p-keminer/iot-alarm-system/hardware/pcb/sender/pcb_sender_r3.png

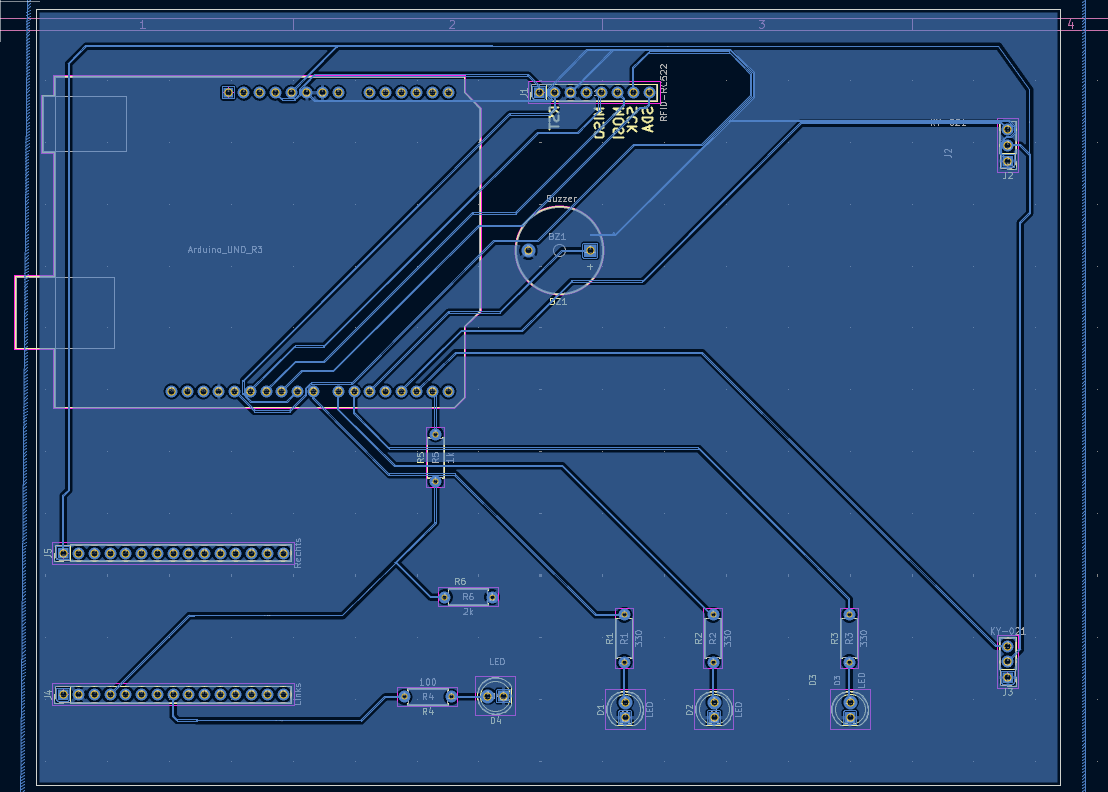
hardware/pcb/sender/pcb_sender_r3.png
