p-keminer/iot-alarm-system/hardware/pcb/sender/pcb_sender_r3_front.png

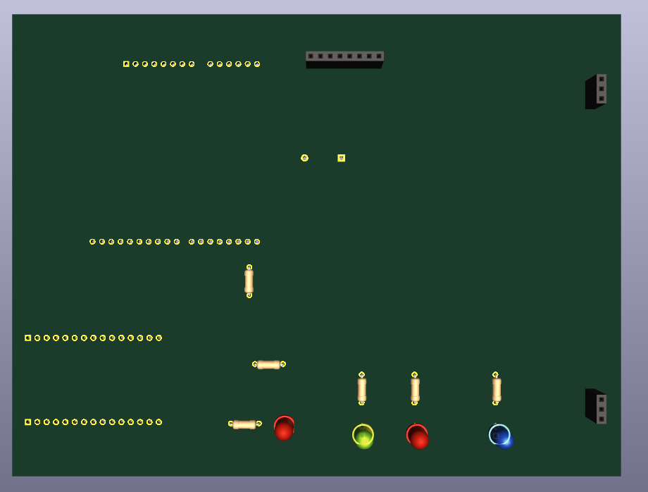
hardware/pcb/sender/pcb_sender_r3_front.png
