p-keminer/iot-alarm-system/hardware/pcb/sender/schematic_sender_r3.png

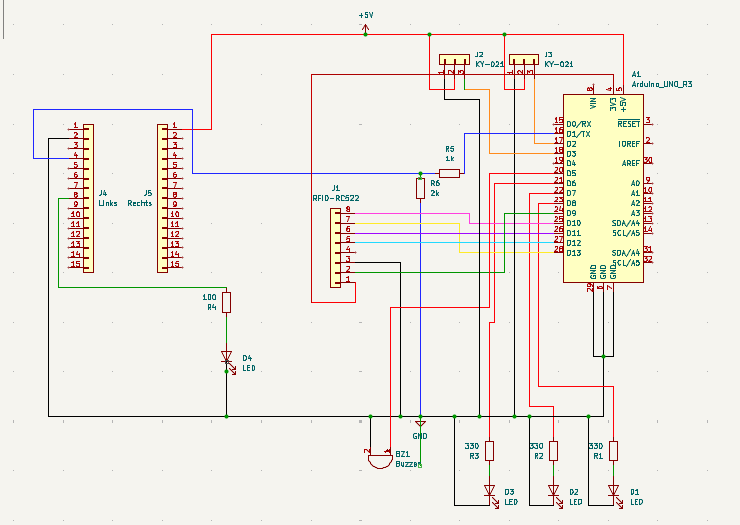
hardware/pcb/sender/schematic_sender_r3.png
