p-keminer/iot-alarm-system/media/photos/prototype_breadboards.png

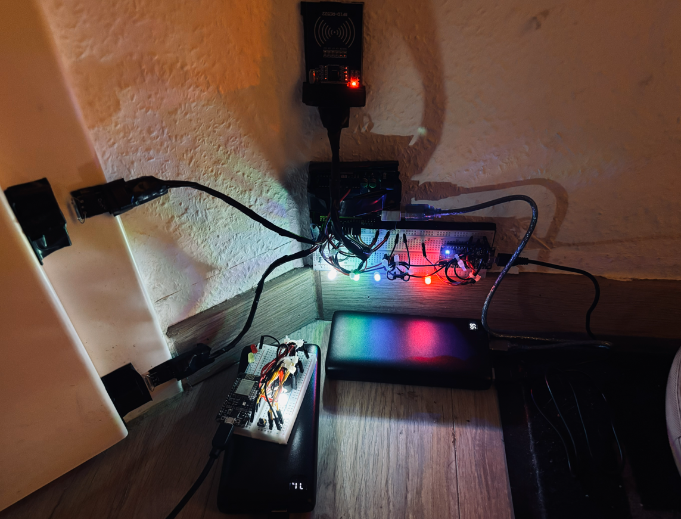
media/photos/prototype_breadboards.png
