p-keminer/iot-alarm-system/media/photos/prototype_housings_3d.jpg

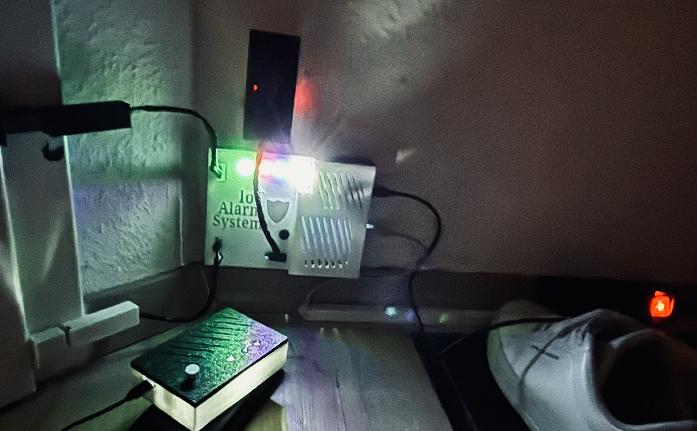
media/photos/prototype_housings_3d.jpg
