p-keminer/iot-alarm-system/media/photos/prototype_perforated_circuit_boards.jpg

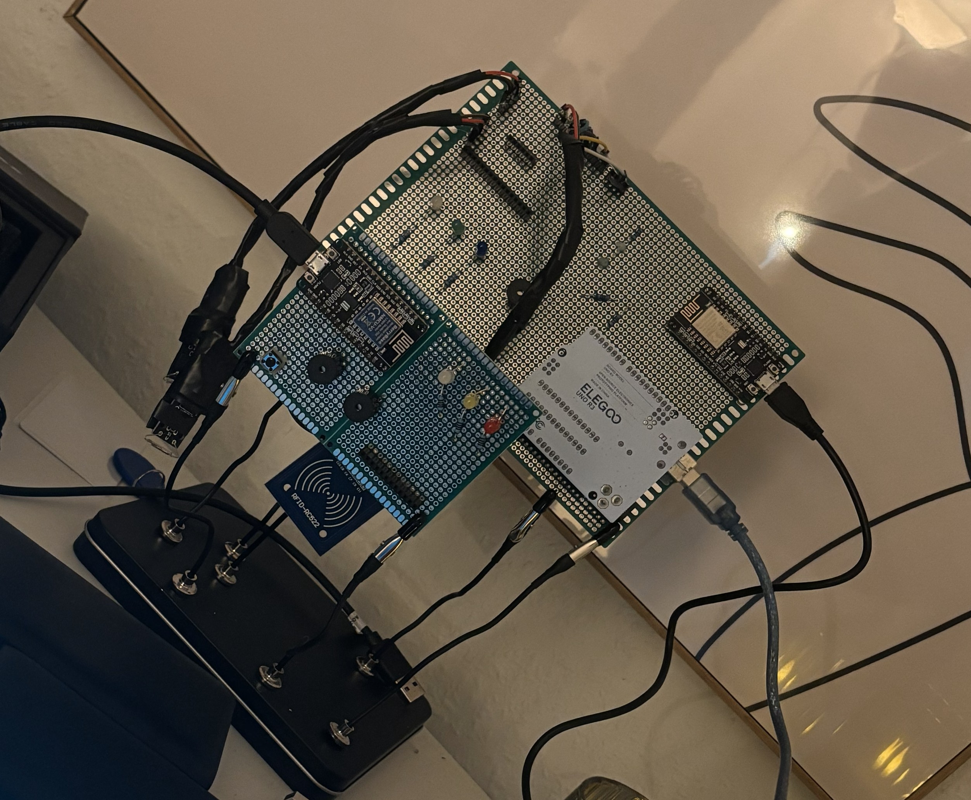
media/photos/prototype_perforated_circuit_boards.jpg
