p-keminer/iot-alarm-system/media/photos/raspberry_pi_zero_2w.jpg

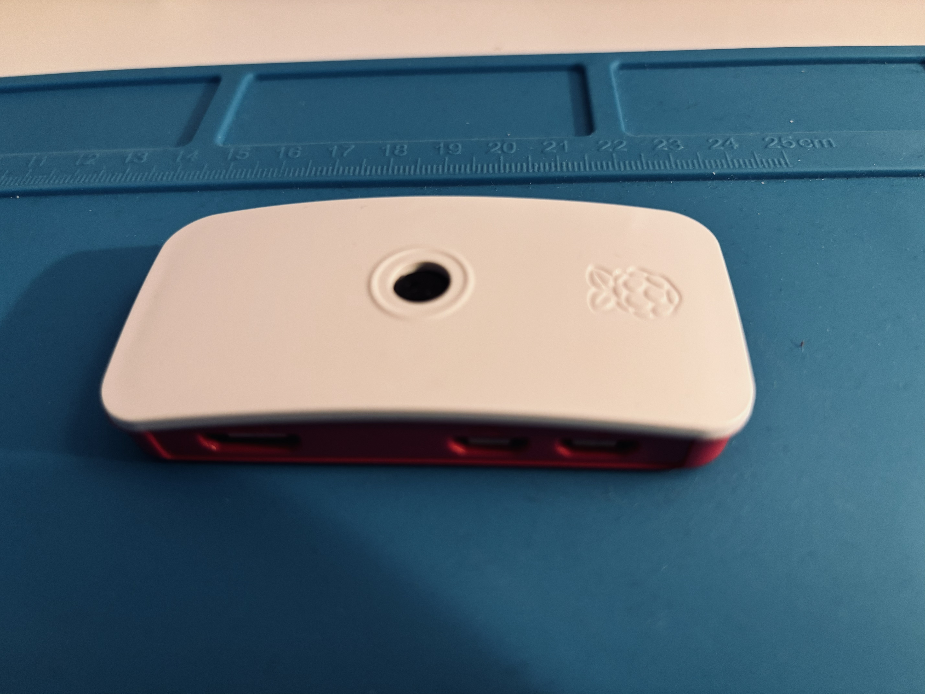
media/photos/raspberry_pi_zero_2w.jpg
