p-keminer/iot-alarm-system/media/photos/raspberrypi.jpg

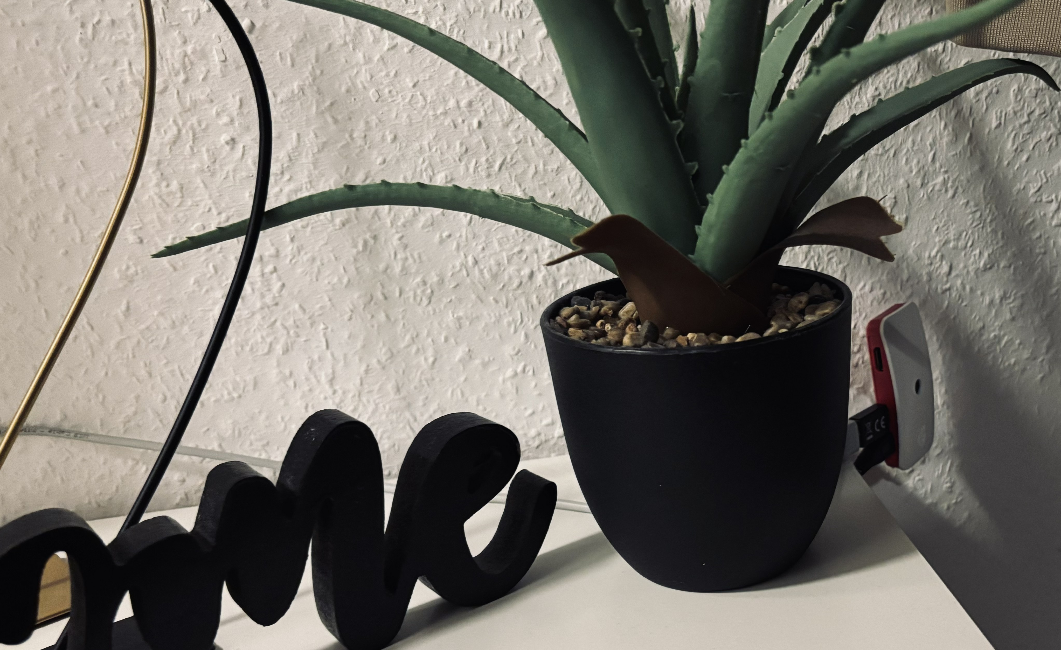
media/photos/raspberrypi.jpg
