p-keminer/iot-alarm-system/media/photos/receiver_enclosure_pcb.jpg

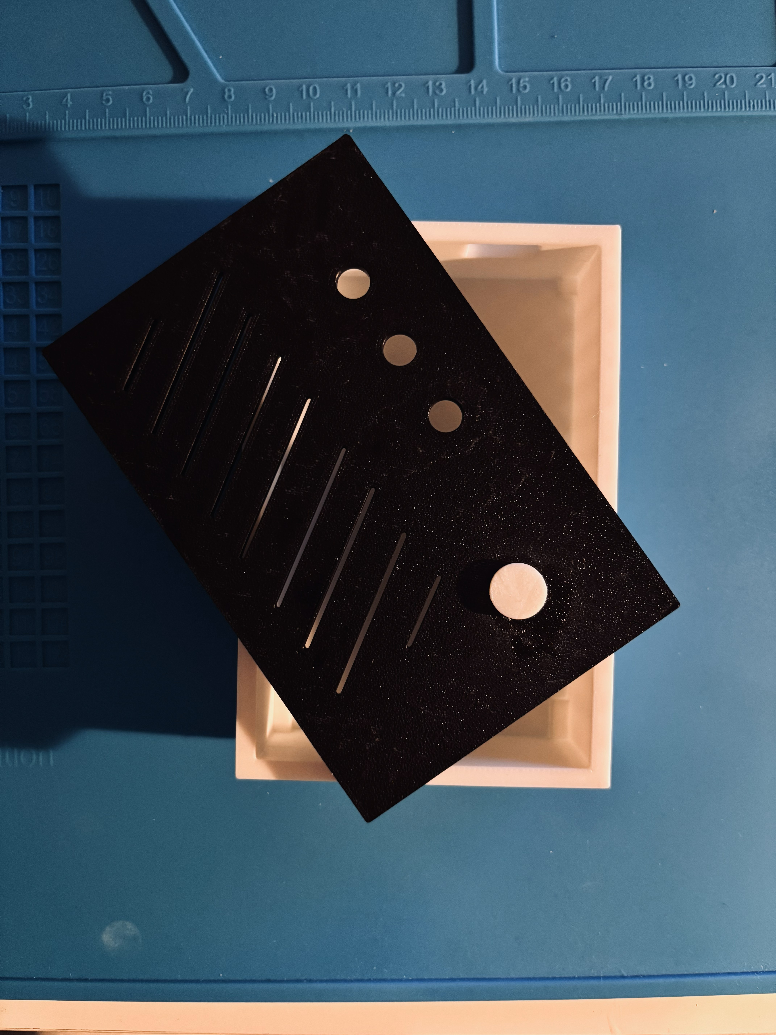
media/photos/receiver_enclosure_pcb.jpg
