p-keminer/iot-alarm-system/media/photos/receiver_pcb.jpg

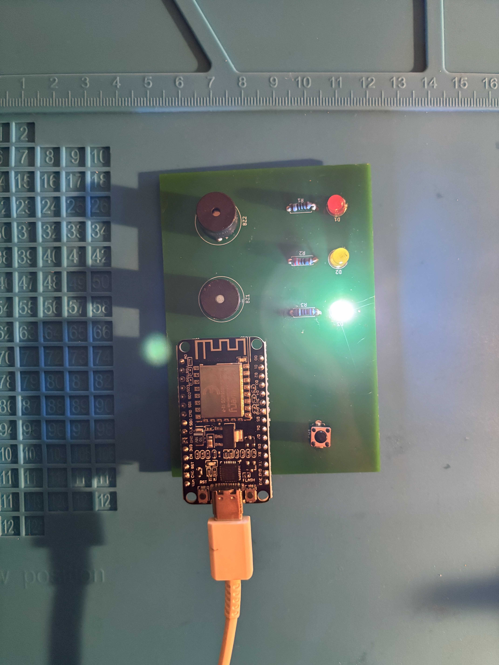
media/photos/receiver_pcb.jpg
