p-keminer/iot-alarm-system/media/photos/sender_enclosure.jpg

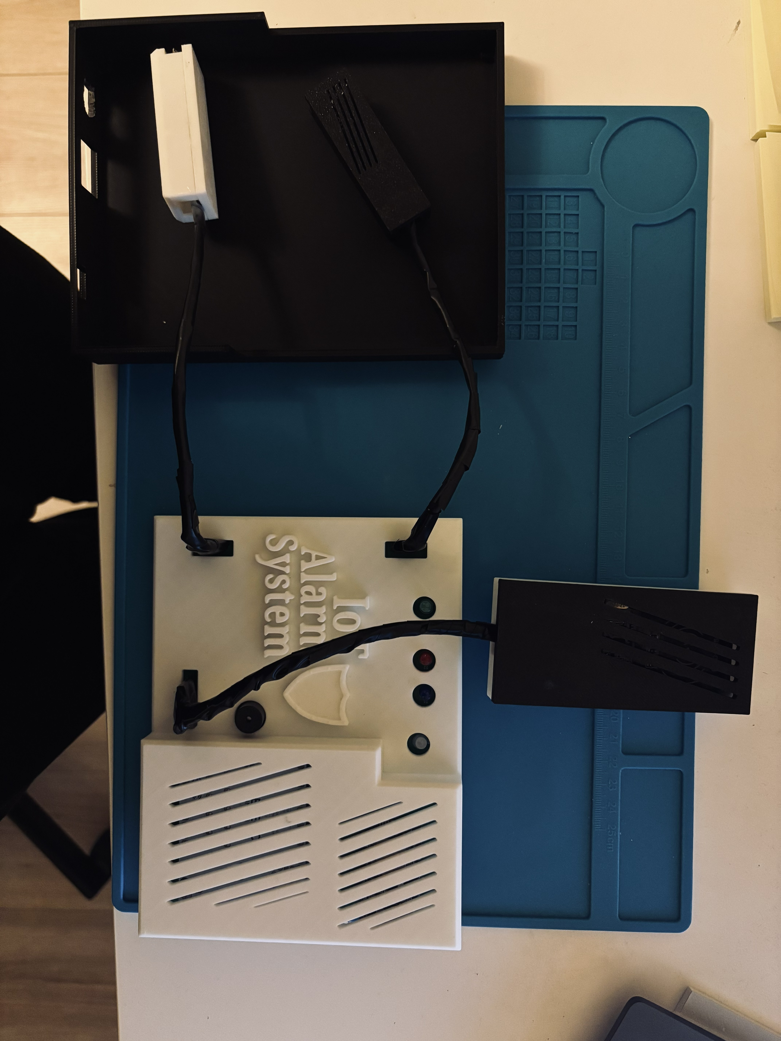
media/photos/sender_enclosure.jpg
