p-keminer/iot-alarm-system/media/photos/sender_pcb.jpg

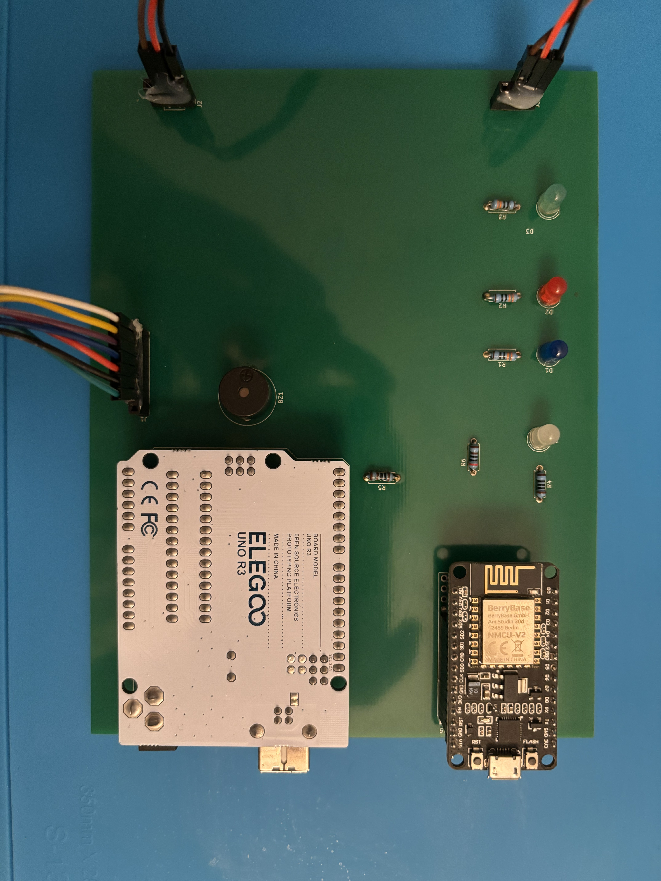
media/photos/sender_pcb.jpg
