p-keminer/iot-alarm-system/media/photos/sensor_enclosure.png

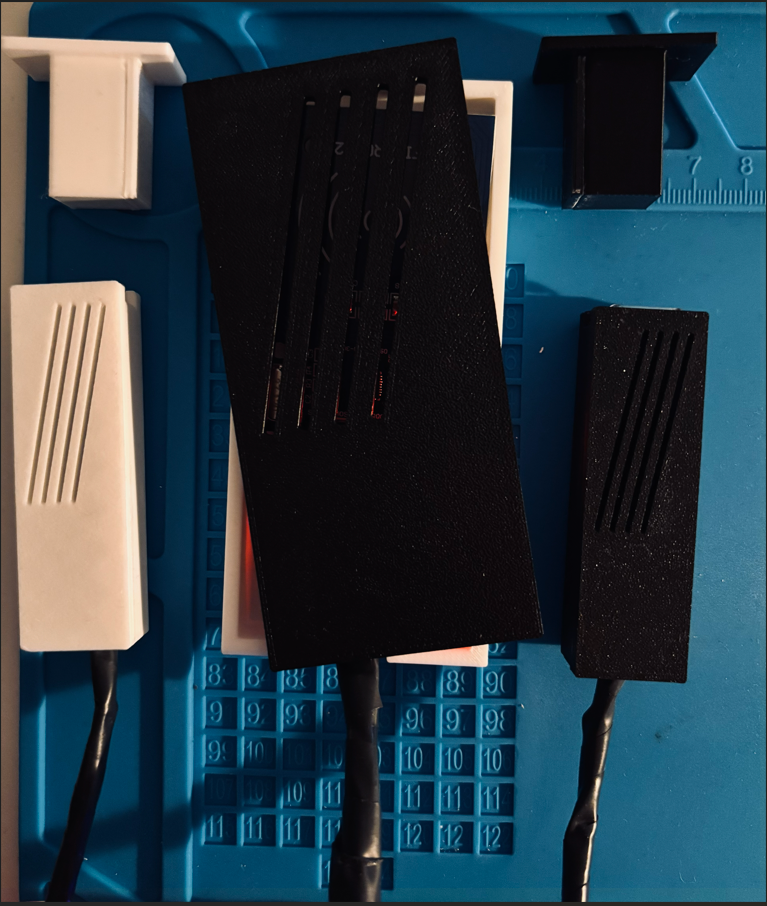
media/photos/sensor_enclosure.png
