p-keminer/iot-alarm-system/media/videos/gifs/receiver_pcb.gif

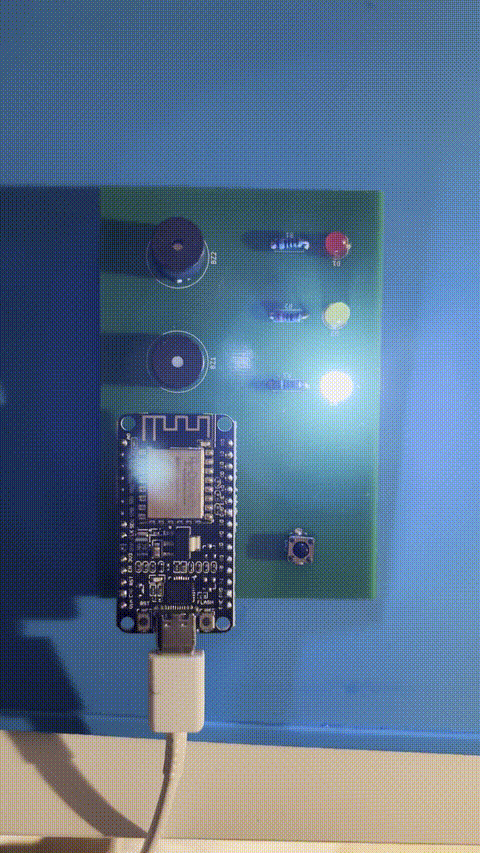
media/videos/gifs/receiver_pcb.gif
