p-keminer/iot-alarm-system/media/videos/gifs/sender_r3_pcb.gif

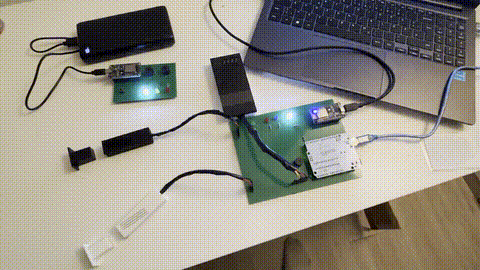
media/videos/gifs/sender_r3_pcb.gif
