p-keminer/iot-alarm-system/mechanics/prints_3d/receiver/receiver_housing.png

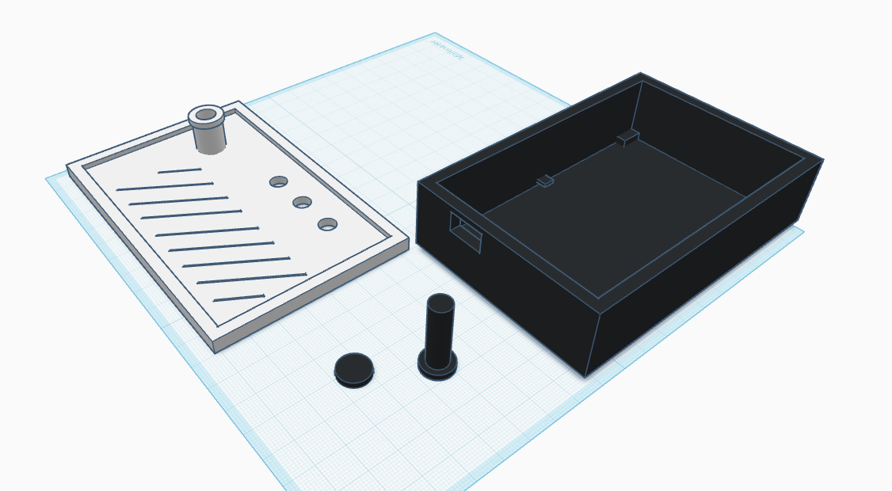
mechanics/prints_3d/receiver/receiver_housing.png
