p-keminer/iot-alarm-system/mechanics/prints_3d/sender/sender_r3_housing.png

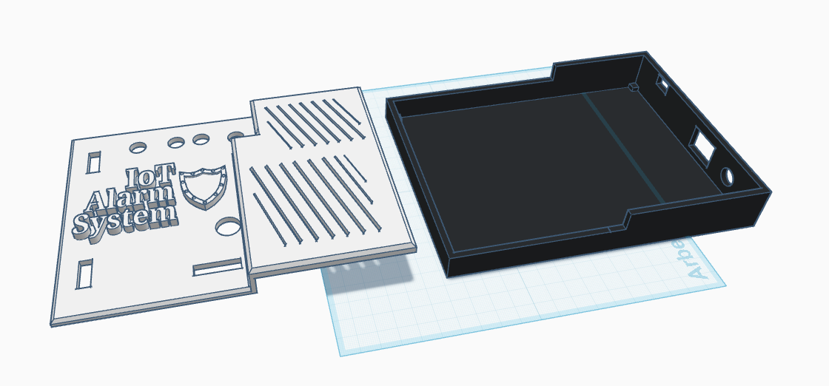
mechanics/prints_3d/sender/sender_r3_housing.png
