p-keminer/iot-alarm-system/firmware/elegoo_uno_r3/sketchR3/alarm_system/hal_rfid.h

// =============================================================================
// hal_rfid.h - Hardwareabstraktion fuer RFID-Leser
// =============================================================================

#ifndef HAL_RFID_H
#define HAL_RFID_H

#include <Arduino.h>

// MFRC522 unterstuetzt 4-, 7- und 10-Byte-UIDs.
#define HAL_RFID_MAX_UID_LEN 10

// Rueckgabewerte beim Kartenlesen
typedef enum {
  RFID_KEINE_KARTE,
  RFID_KARTE_GELESEN,
  RFID_LESEFEHLER
} RfidStatus;

// Initialisierung
void hal_rfid_init();

// Karte lesen, UID in Puffer schreiben
RfidStatus hal_rfid_leseKarte(byte* uidPuffer, byte* uidLaenge);

// Kommunikation mit Karte beenden
void hal_rfid_beenden();

#endif
